mijuc/CCFL2LED/pictures/CCFL2LEDfinal2.png

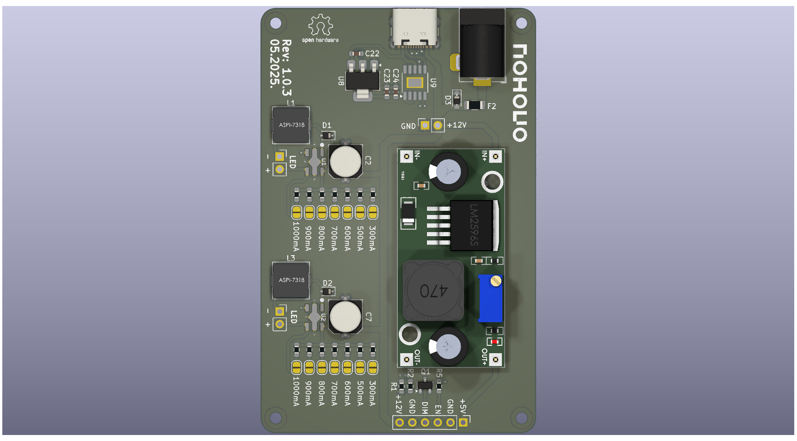
pictures/CCFL2LEDfinal2.png
