mijuc/CCFL2LED/pictures/prototip1.jpg

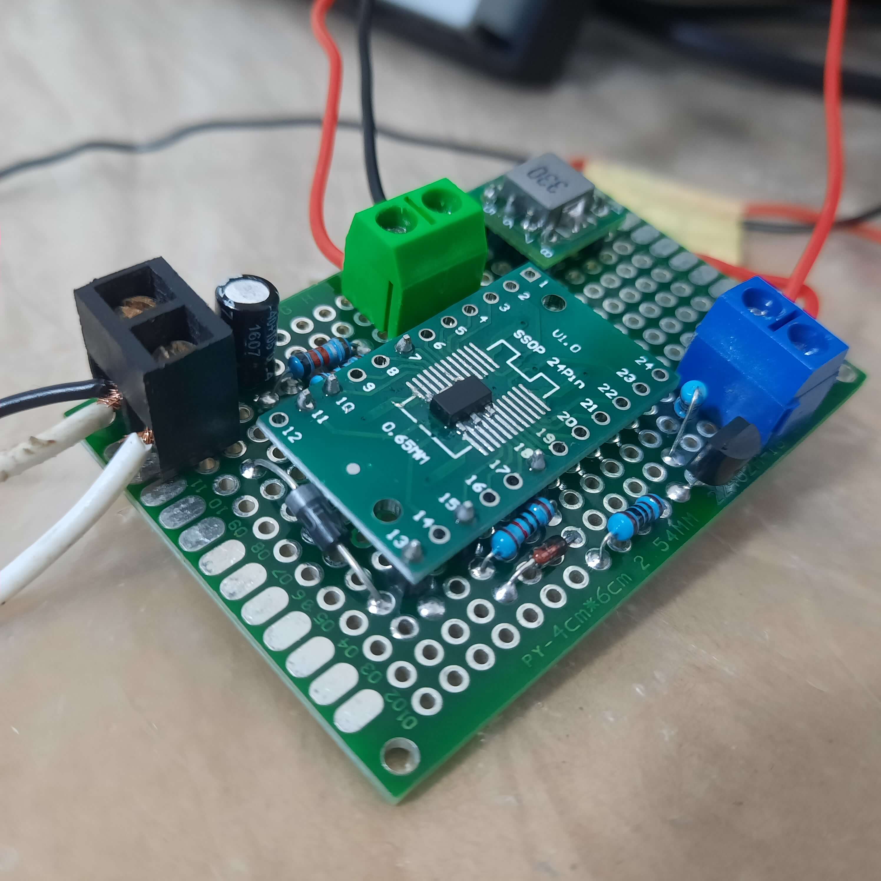
pictures/prototip1.jpg
