mijuc/CCFL2LED/pictures/Vertical2.png

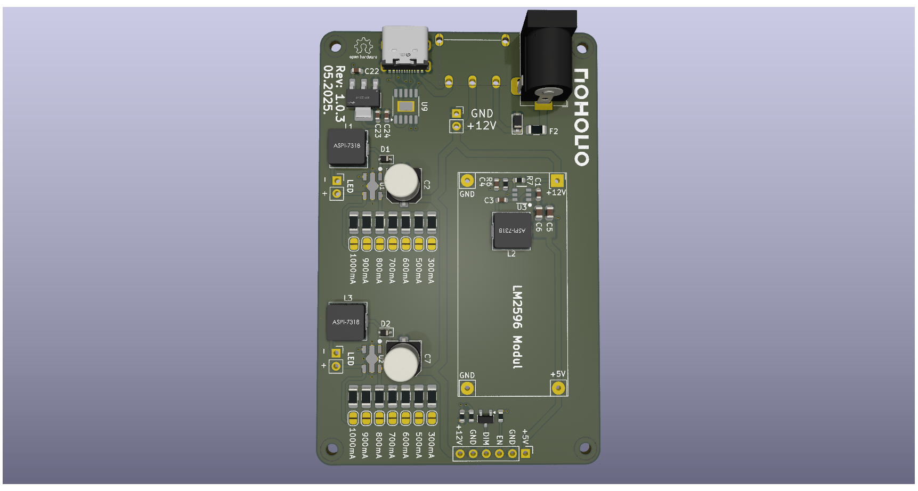
pictures/Vertical2.png
