mijuc/CCFL2LED/pictures/Vertical.png

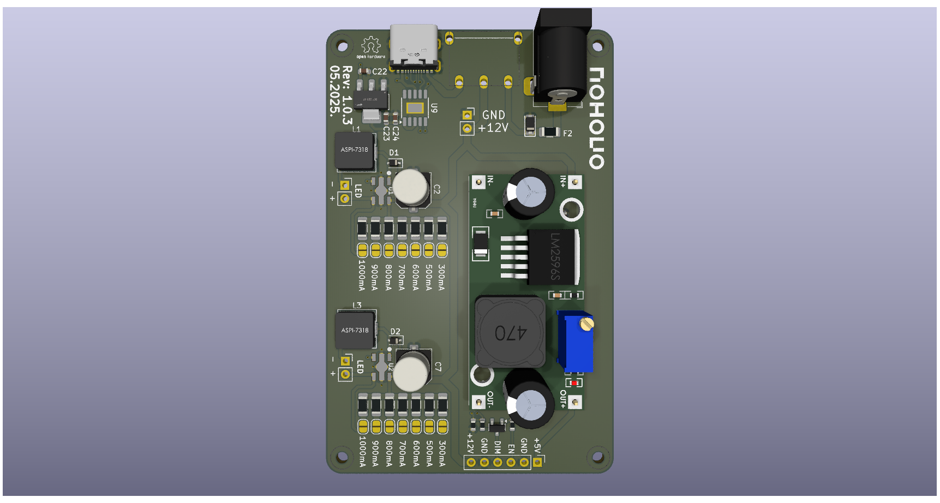
pictures/Vertical.png
