mijuc/CCFL2LED/pictures/step4_2.jpg

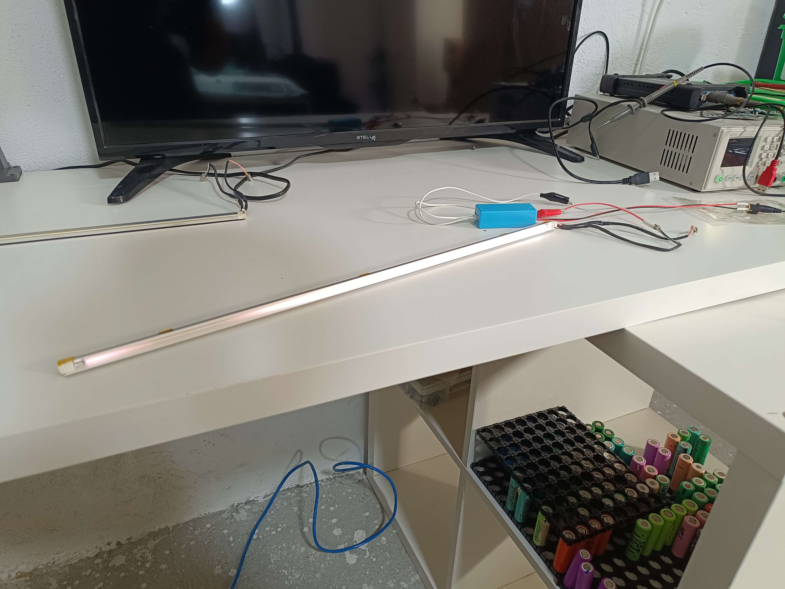
pictures/step4_2.jpg
