mijuc/CCFL2LED/pictures/step7_2.jpg

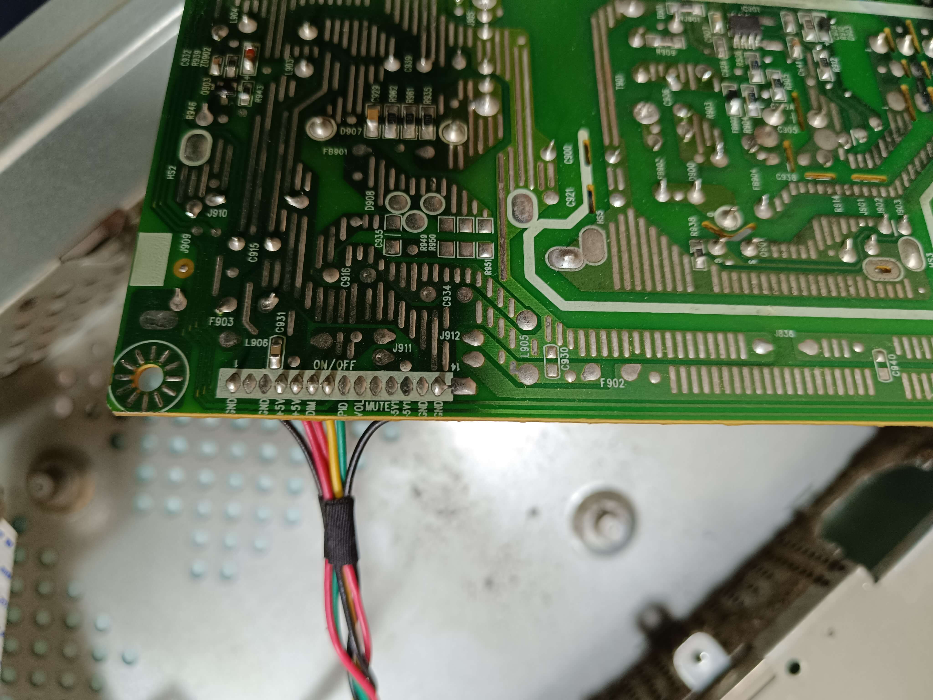
pictures/step7_2.jpg
