mijuc/CCFL2LED/pictures/step8_2.jpg

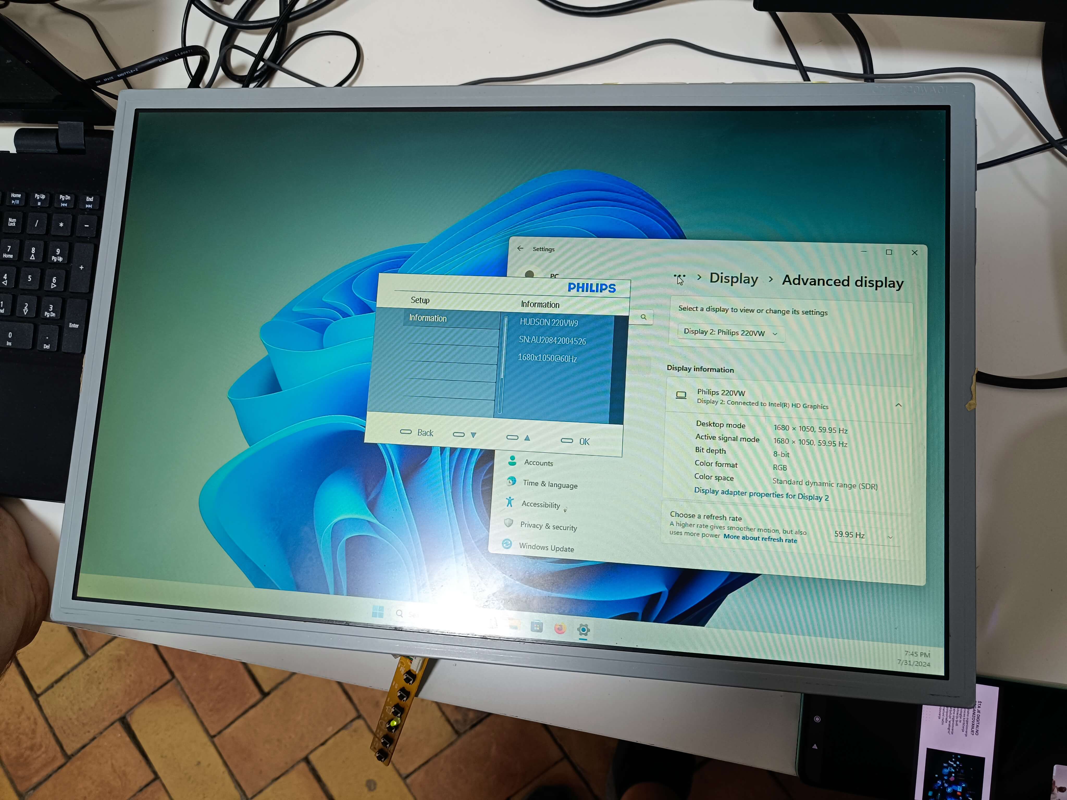
pictures/step8_2.jpg
